ZIRoberts/Wireless-Graphical-Visualizer/Single Stage Circuit Sim/Single Stage - TLV2372.asc

B1: bv; V=V(sine)*V(pulse)
C3: cap; {C3_val}
C4: cap; {C4_val}
C9: cap; 22µ
C10: cap; {C10_val}
C500: cap; .1µ
C501: cap; 100µ
C502: cap; 100µ
D1: diode; PMEG2005EGW
D2: schottky; BAT54
D3: diode; 1N4148
R1: res; {R1_val}; tol=1
R2: res; {R2_val}; tol=1
R3: res; 10k
R5: res; {R5_val}; tol=1
R9: res; {R9_val}; tol=5
R500: res; 49900; tol=1
R501: res; 49900; tol=1
R510: res; 2k; tol=5
R511: res; 2k; tol=5
U1: opamp2; TLV2372
U5: LT1639
V1: signal; SINE(0 1.1 {fin}); AC 1
V2: voltage; 5
V3: voltage; PULSE(0 1 25m 1u 1u 90m 150m)
V4: voltage; 2.5
Named nets: 0, Vcc, vgnd, amp, op_out, rect, Vin, rect_in, sine, Pulse, Burst
;.step param fin list 63, 400, 1000, 2000, 2500, 3000, 4000, 5000
;.step param fin list 400, 1000, 2000, 2500, 3000, 4000,5000, 6000, 6500
;.param fin=6502
;.tran 0.5
;.ac dec 5 60 1000000
.param x=7 ;index to table
.param fin         table(x, 1,   160,  2,  250 ,  3,    400, 4,     650, 5,   1000,  6,  2500, 7,   4000, 8, 6500) ; Hertz
.param R1_val table(x, 1, 1250, 2,  7500, 3,   7500, 4,   4990, 5, 10000, 6,  7500, 7,  10000, 8, 4699)
.param R2_val table(x, 1,    267, 2,   267, 3,     402, 4,     267, 5,     806, 6,    301, 7,      348, 8,    267)
.param C3_val table(x, 1,      1u, 2,  0.2u, 3,  0.1u, 4,    0.1u, 5,  0.02u, 6,  0.02u, 7,  0.01u, 8,  0.01u)
.param C4_val table(x, 1,      1u, 2,  0.2u, 3,  0.1u, 4,    0.1u, 5,  0.02u, 6,  0.02u, 7,  0.01u, 8,  0.01u)
.param R5_val table(x, 1,  6040, 2, 35700, 3, 40200, 4, 23700, 5, 54900, 6, 34800, 7, 47500, 8, 23530)
.meas TRAN Myamp_RMS RMS V(op_out) FROM 50m TO 100m
.meas TRAN Myop_out_RMS RMS V(op_out) FROM 50m TO 100m
.meas TRAN MyRect_RMS AVG V(rect) FROM 50m TO 100m
.meas tran MyFreq param fin
.meas tran MyR1 param R1_val
.meas tran MyR2 param R2_val
.meas tran MyC3 param C3_val
.meas tran MyC4 param C4_val
.meas tran MyR5 param R5_val
;.step param x 1 8 1
.lib TLV2372.lib
.options gmin = 1e-10
.options abstol=1e-10
.options cshunt=1e-15
.options reltol=0.003
SIMULATION OPTIONS
LTspice Converge Fixers
External Sub Circuits
Measure Nodes, See Spice Error Logs for Results
Bandpass Circuit Selection
Save Parameters corresponding to Measurements
.param C10_val table(x,1,  0.22u, 2, 0.22u, 3, 0.22u, 4, 0.22u, 4, 0.22u, 5, 0.22u, 6, .1u, 7, 0.1u, 8, 0.1u)
.param R9_val table (x, 1, 375000, 2, 255000, 3, 255000, 4, 200000, 5, 200000, 6, 100000, 7, 100000, 8, 100000)
Vclamp
.tran 0 10.05 9.8
.lib PMEG2005EGW.txt
